tomatosoupcan/mino/photos/headers_connected.png

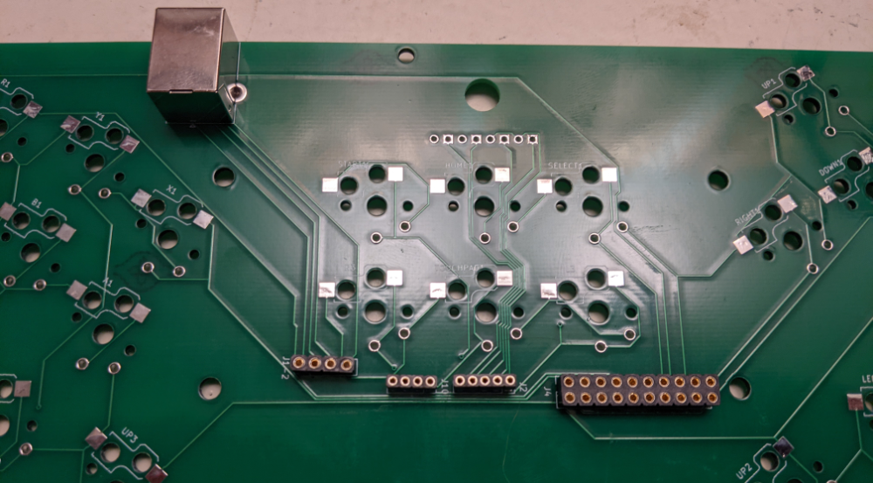
photos/headers_connected.png
